BojanSof/at2usb/at2usbClassic.X/ps2usb.c

#include "ps2usb.h"

static const uint8_t ps2UsbMap[] = {
    0x00,
    0x42, //F9
    0x00,
    0x3E, //F5
    0x3C, //F3
    0x3A, //F1
    0x3B, //F2
    0x45, //F12
    0x00,
    0x43, //F10
    0x41, //F8
    0x3F, //F6
    0x3D, //F4
    0x2B, //TAB
    0x35, //'`'
    0x00,
    0x00,
    0xE2, //Left ALT
    0xE1, //LEFT shift
    0x00,
    0xE0, //Left ctrl
    0x14, //'q'
    0x1e, //'1'
    0x00,
    0x00,
    0x00,
    0x1d, //z
    0x16, //s
    0x04, //a
    0x1a, //w
    0x1f, //z
    0x00,
    0x00,
    0x06, //c
    0x1b, //x
    0x07, //d
    0x08, //e
    0x21, //4
    0x20, //3
    0x00,
    0x00,
    0x2c, //SPACE ' '
    0x19, //v
    0x09, //f
    0x17, //t
    0x15, //r
    0x22, //5
    0x00,
    0x00,
    0x11, //n
    0x05, //b
    0x0b, //h
    0x0a, //g
    0x1c, //y
    0x23, //6
    0x00,
    0x00,
    0x00,
    0x10, //m
    0x0d, //j
    0x18, //u
    0x24, //7
    0x25, //8
    0x00,
    0x00,
    0x36, //',' 
    0x0e, //k
    0x0c, //i
    0x12, //o
    0x27, //0
    0x26, //9
    0x00,
    0x00,
    0x37, //'.'
    0x38, //'/'
    0x0f, //l
    0x33, //';'
    0x13, //p
    0x2d, //'-'
    0x00,
    0x00,
    0x00,
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
    0x39, //Caps lock
    0xE5, //Rshift
    0x28, //Enter
    0x30, //']'
    0x00,
    0x31, //'\\'
    0x00,
    0x00,
    0x00,
    0x00,
    0x00,
    0x00,
    0x00,
    0x00,
    0x2A, //Backspace
    0x00,
    0x00,
    0x1e, //'1'
    0x00,
    0x21, //'4'
    0x24, //'7'
    0x00,
    0x00,
    0x00,
    0x27, //'0'
    0x37, //'.'
    0x1f, //'2'
    0x22, //'5'
    0x23, //'6'
    0x25, //8
    0x29, //ESCAPE
    0x53, //Num lock
    0x44, //F11
    0x2e, //'+'
    0x20, //'3'
    0x2d, //'-'
    0x25, //'*'
    0x26, //'9'
    0x00, //Scroll
    0x00,
    0x00,
    0x00,
    0x00,
    0x40 //F7 
};

static const uint8_t ps2ExtUsbMap[] = {
    0x00,
    0x00,
    0x00,
    0x00,
    0x00,
    0x00,
    0x00,
    0x00,
    0x00,
    0x00,
    0x00,
    0x00,
    0x00,
    0x00,
    0x00,
    0x00,
    0x00,
    0xe6,
    0x00,
    0x00,
    0xe4,
    0x00,
    0x00,
    0x00,
    0x00,
    0x00,
    0x00,
    0x00,
    0x00,
    0x00,
    0x00,
    0xe3,
    0x00,
    0x00,
    0x00,
    0x00,
    0x00,
    0x00,
    0x00,
    0xe7,
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
};

uint8_t PS2USB_ScanCodeToUSBHID(const PS2ScanCode *scanCode) {
    if (scanCode->isExtend) {
        return ps2ExtUsbMap[scanCode->value];
    } else {
        return ps2UsbMap[scanCode->value];
    }
}
